inetrg/inet-mbh/resources/bh-full-top.jpg

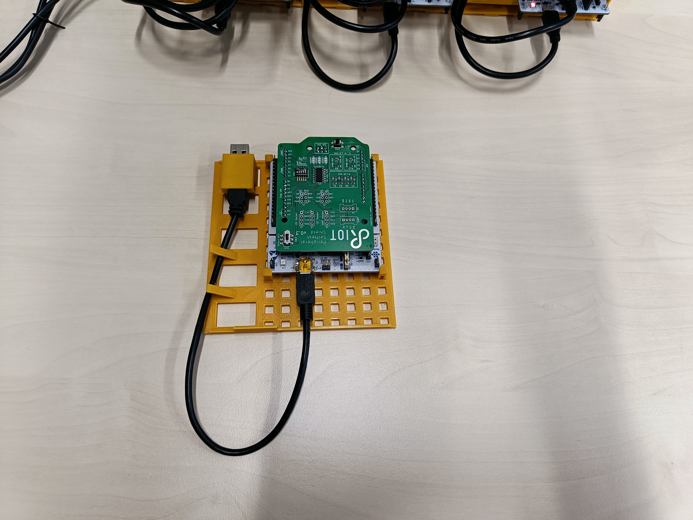
resources/bh-full-top.jpg
