inetrg/inet-mbh/resources/manufacturing.jpg

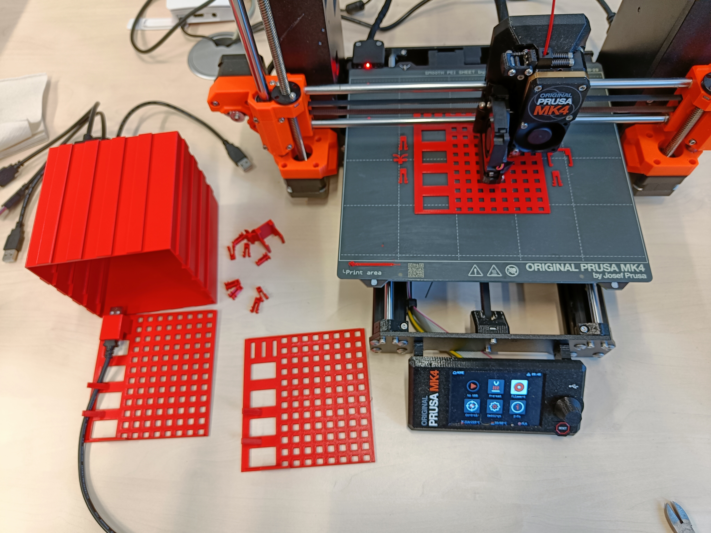
resources/manufacturing.jpg
